ICantMakeThings/NiceTOTP/images/46.JPG

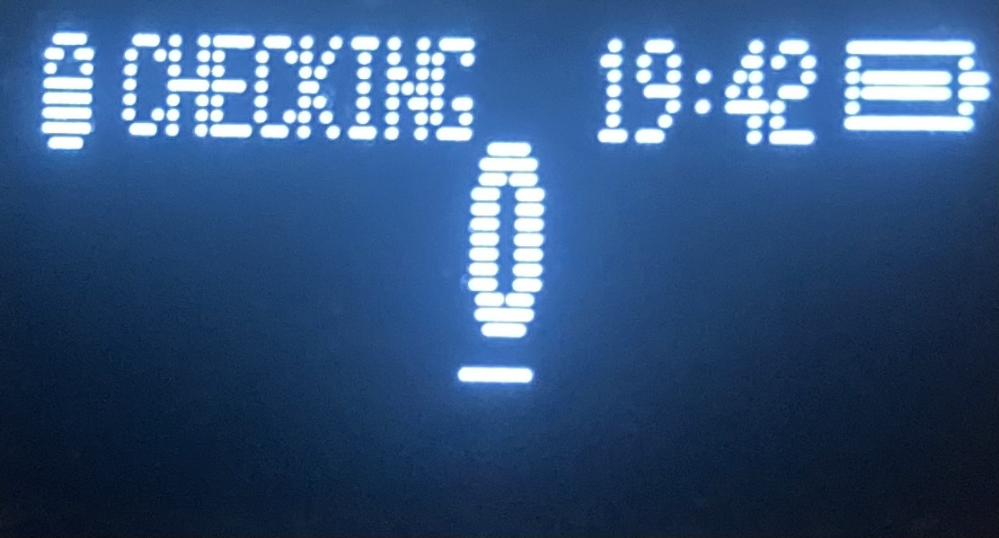
images/46.JPG
